SahanDissanayaka/Robot-Design-for-SLRC/Robo Arm/overall arm.SLDASM

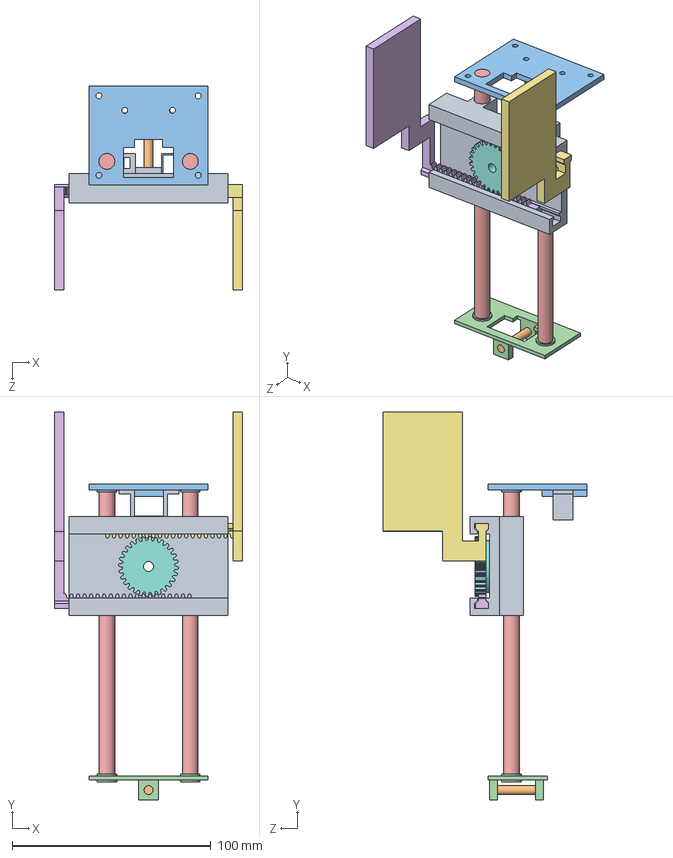
[picture p2: CAD file, 2024-04-25]
Robo Arm/overall arm.SLDASM
94.9 x 195.3 x 102.8 mm
base
Pinion Gear, Large Version
Pusher, 75mm Long left
Pusher, 75mm Long right
rod left x 2
upper base
lower base
pin upper
motor clip
