SahanDissanayaka/Robot-Design-for-SLRC/Robo Arm/Pusher, 75mm Long left.SLDPRT

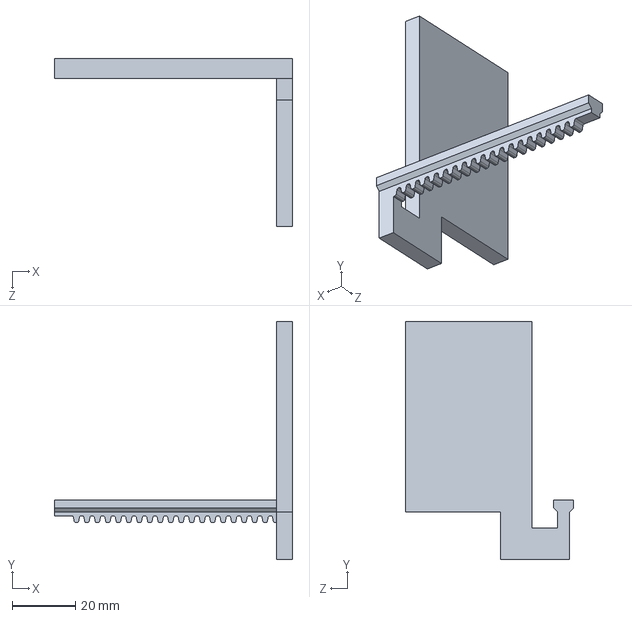
[picture p16: CAD file, 2024-04-25]
Robo Arm/Pusher, 75mm Long left.SLDPRT
75.0 x 75.0 x 53.1 mm
