SahanDissanayaka/Robot-Design-for-SLRC/SolidWorks/Enclosure/M3 Spacer MF 30mm.SLDPRT

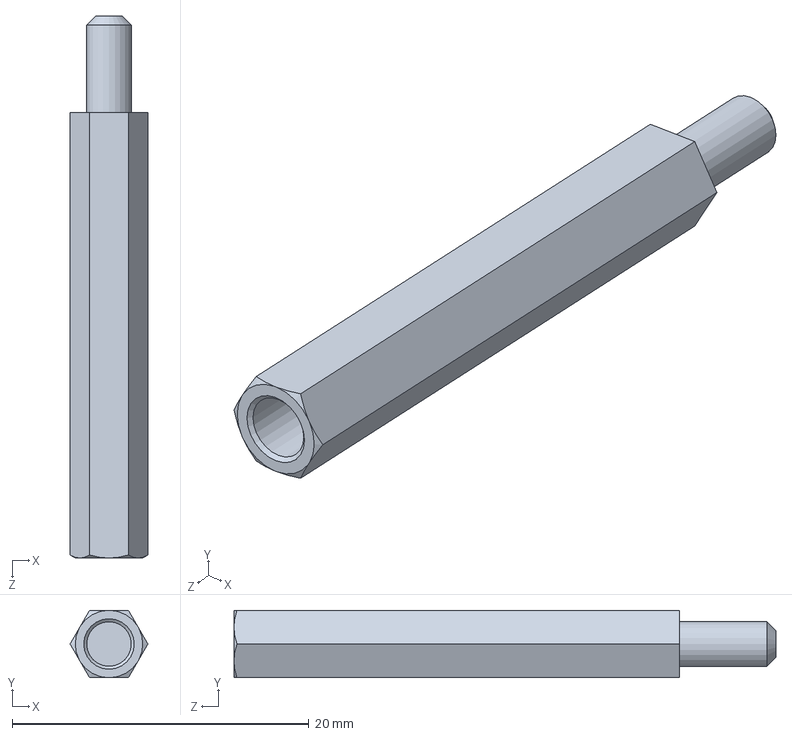
[picture p17: CAD file, 2024-04-28]
SolidWorks/Enclosure/M3 Spacer MF 30mm.SLDPRT
5.24 x 4.54 x 36.5 mm
