SahanDissanayaka/Robot-Design-for-SLRC/Robo Arm/motor clip.SLDPRT

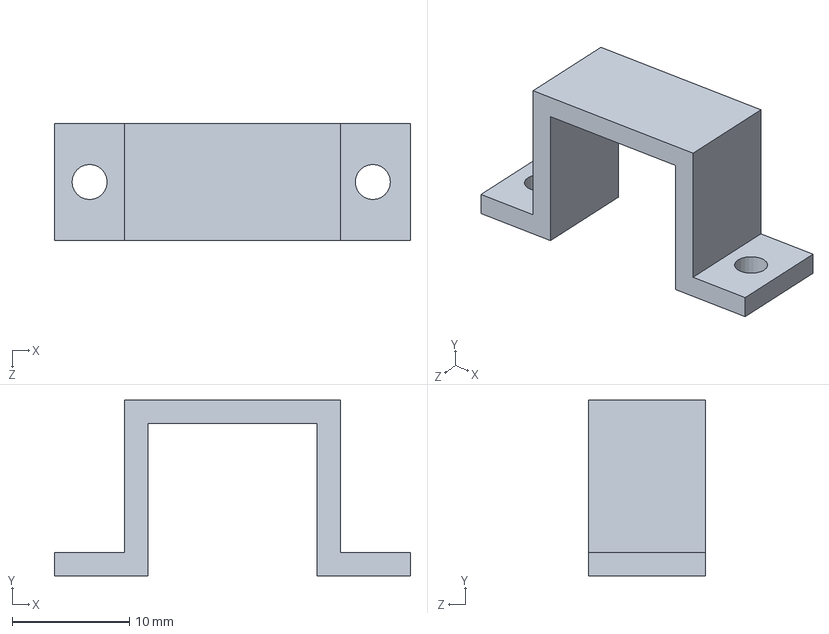
[picture p18: CAD file, 2024-04-25]
Robo Arm/motor clip.SLDPRT
30.4 x 15.0 x 10.0 mm
