SahanDissanayaka/Robot-Design-for-SLRC/SolidWorks/Enclosure/HCSR04 Ultrasonic Sensor.SLDPRT

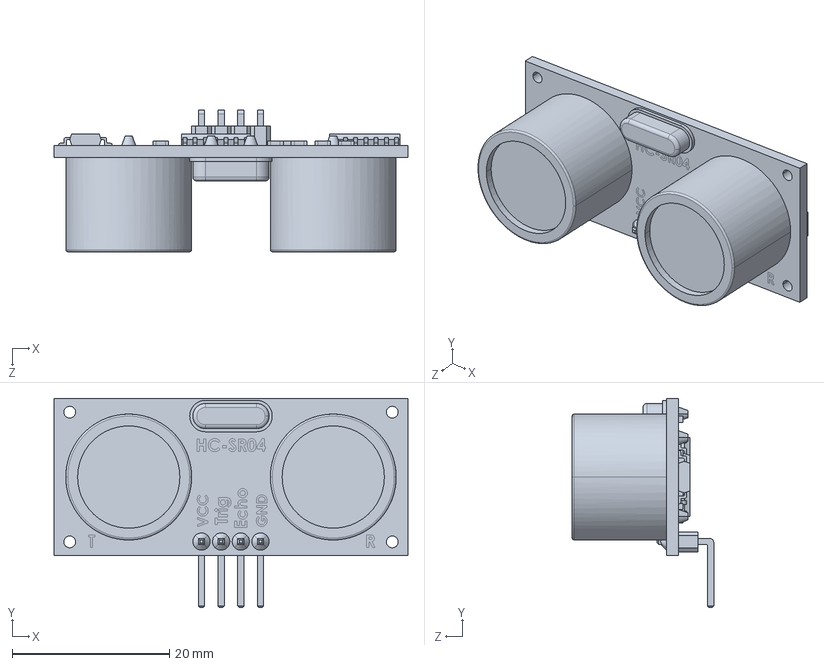
[picture p19: CAD file, 2024-04-28]
SolidWorks/Enclosure/HCSR04 Ultrasonic Sensor.SLDPRT
45.0 x 26.6 x 18.0 mm
