SahanDissanayaka/Robot-Design-for-SLRC/SolidWorks/Enclosure/IR holder.SLDPRT

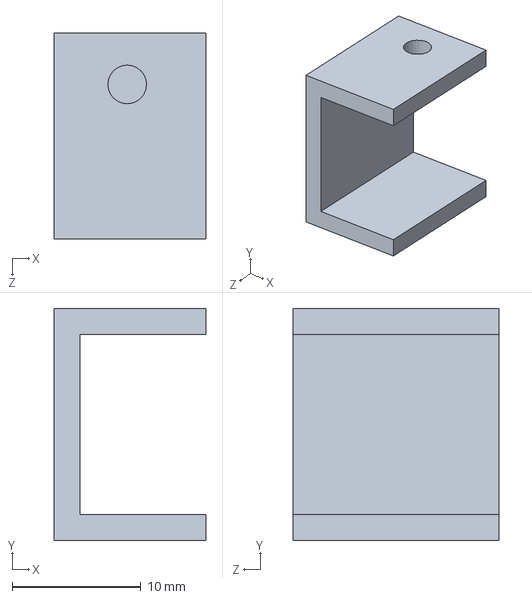
[picture p20: CAD file, 2024-04-28]
SolidWorks/Enclosure/IR holder.SLDPRT
11.8 x 18.0 x 16.0 mm
