SahanDissanayaka/Robot-Design-for-SLRC/Robo Arm/lower base.SLDPRT

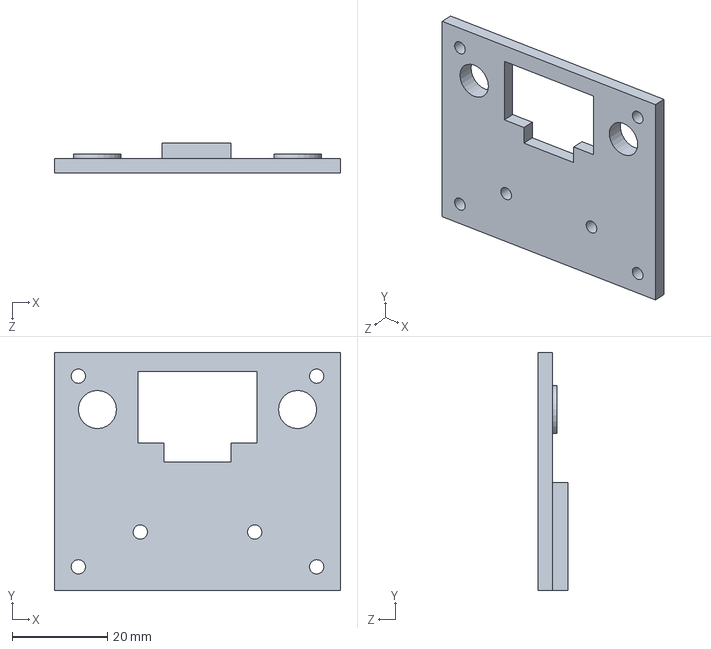
[picture p21: CAD file, 2024-04-25]
Robo Arm/lower base.SLDPRT
60.0 x 50.0 x 6.30 mm
