SahanDissanayaka/Robot-Design-for-SLRC/SolidWorks/Enclosure/ToF Holder.SLDPRT

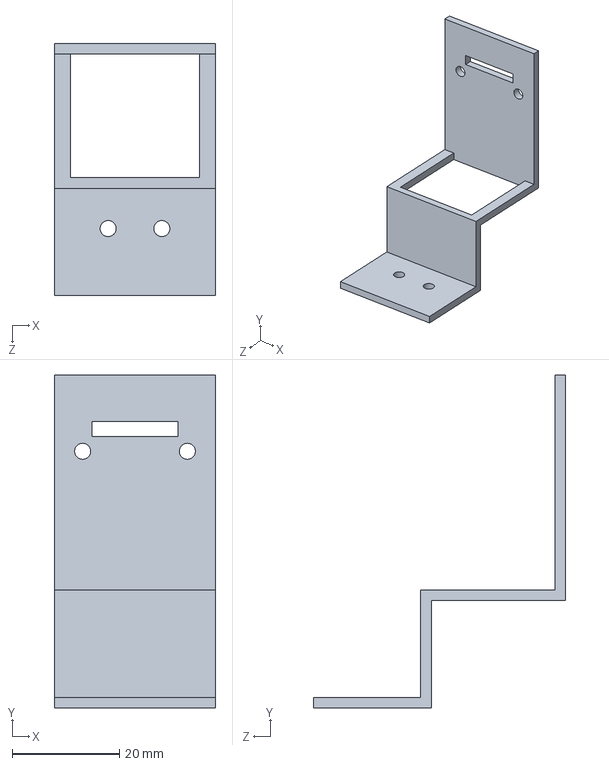
[picture p22: CAD file, 2024-04-28]
SolidWorks/Enclosure/ToF Holder.SLDPRT
30.0 x 62.0 x 47.0 mm
