SahanDissanayaka/Robot-Design-for-SLRC/Robo Arm/base.SLDPRT

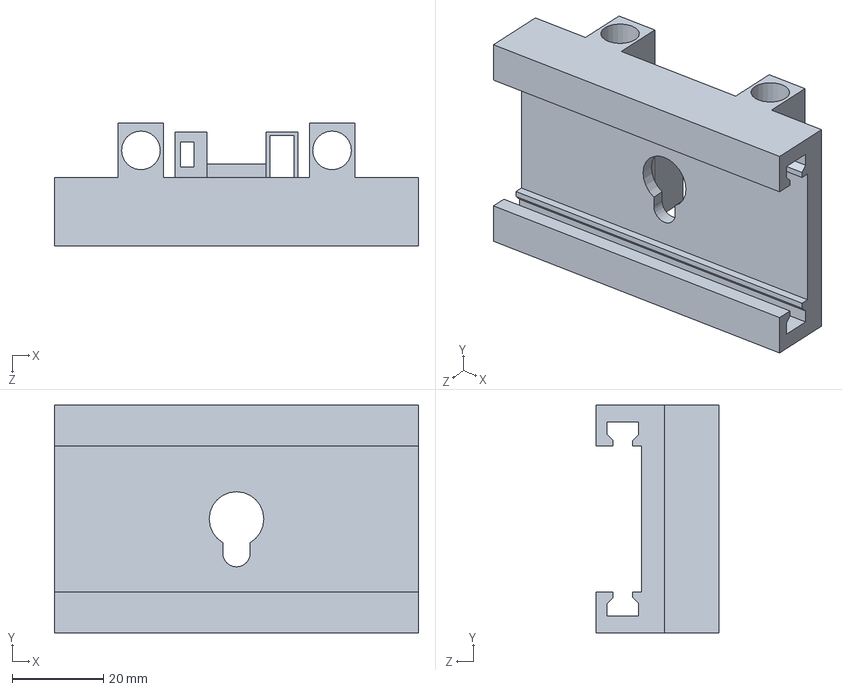
[picture p23: CAD file, 2024-04-25]
Robo Arm/base.SLDPRT
80.0 x 50.0 x 27.0 mm
