SahanDissanayaka/Robot-Design-for-SLRC/SolidWorks/Enclosure/Ultrasonic Holder.SLDPRT

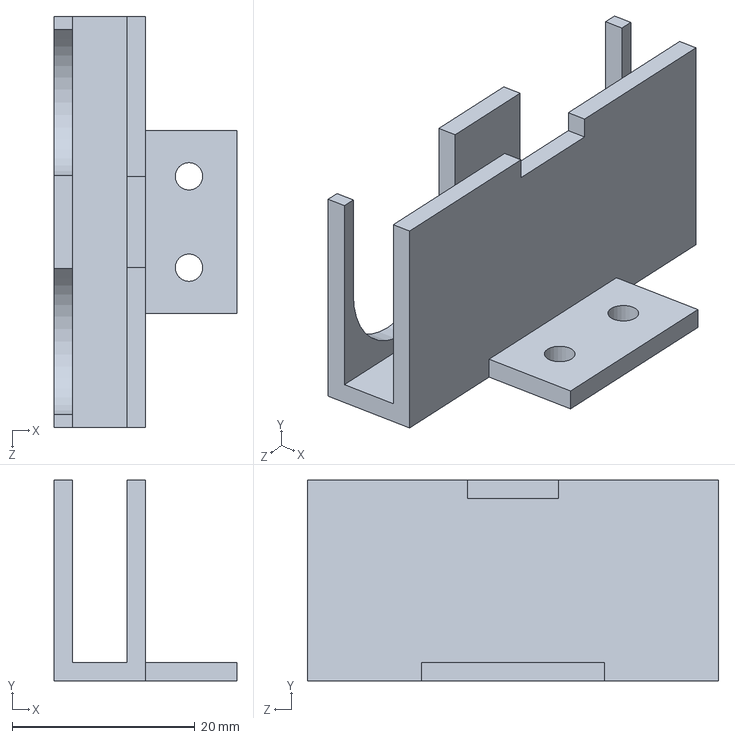
[picture p24: CAD file, 2024-04-28]
SolidWorks/Enclosure/Ultrasonic Holder.SLDPRT
20.0 x 22.0 x 45.0 mm
