SahanDissanayaka/Robot-Design-for-SLRC/Robo Arm/Pusher, 75mm Long right.SLDPRT

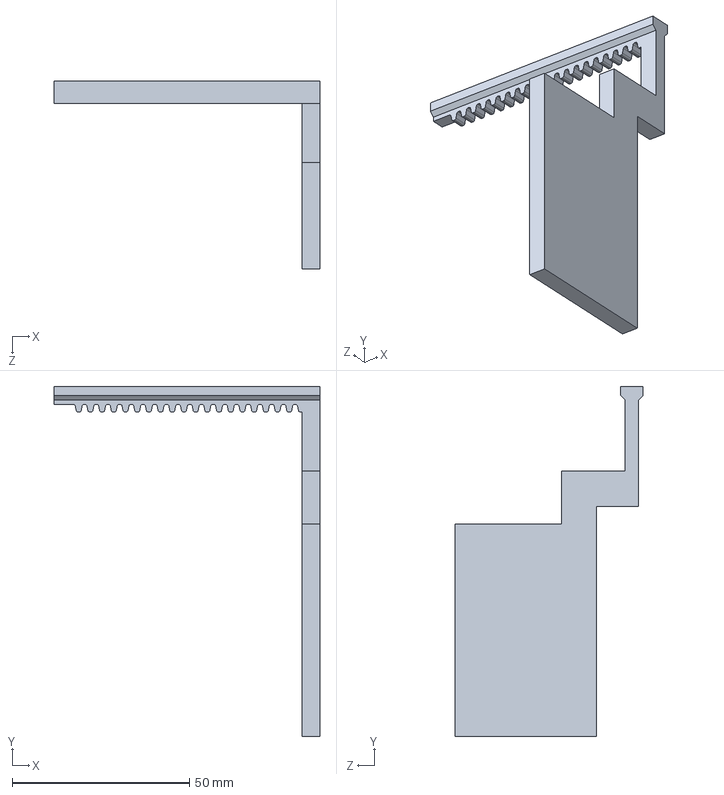
[picture p25: CAD file, 2024-04-25]
Robo Arm/Pusher, 75mm Long right.SLDPRT
75.0 x 98.8 x 53.1 mm
