SahanDissanayaka/Robot-Design-for-SLRC/SolidWorks/Enclosure/Top Part.SLDPRT

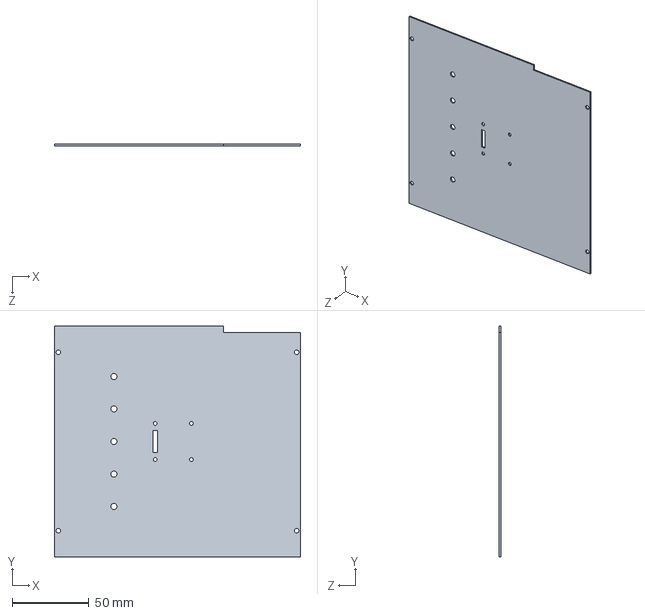
[picture p26: CAD file, 2024-04-28]
SolidWorks/Enclosure/Top Part.SLDPRT
160.0 x 150.0 x 1.00 mm
