SahanDissanayaka/Robot-Design-for-SLRC/Robo Arm/upper base.SLDPRT

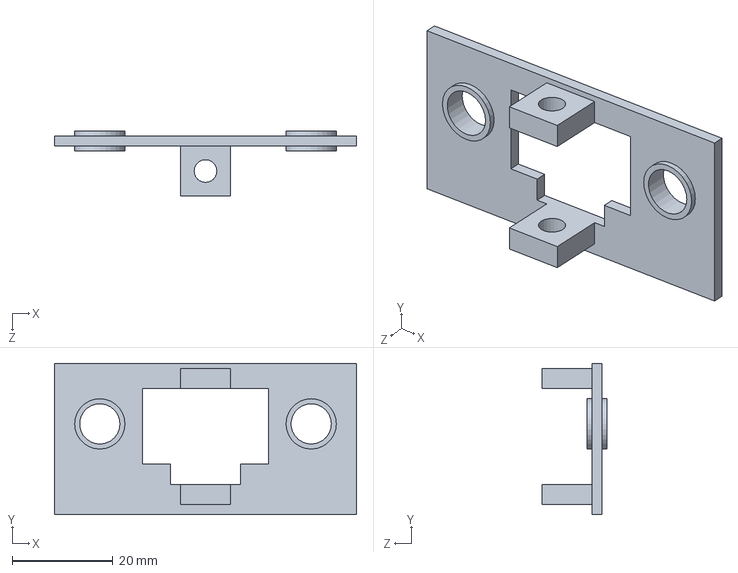
[picture p27: CAD file, 2024-04-25]
Robo Arm/upper base.SLDPRT
60.0 x 30.0 x 13.0 mm
