SahanDissanayaka/Robot-Design-for-SLRC/SolidWorks/Enclosure/TCS3200 color sensor.SLDPRT

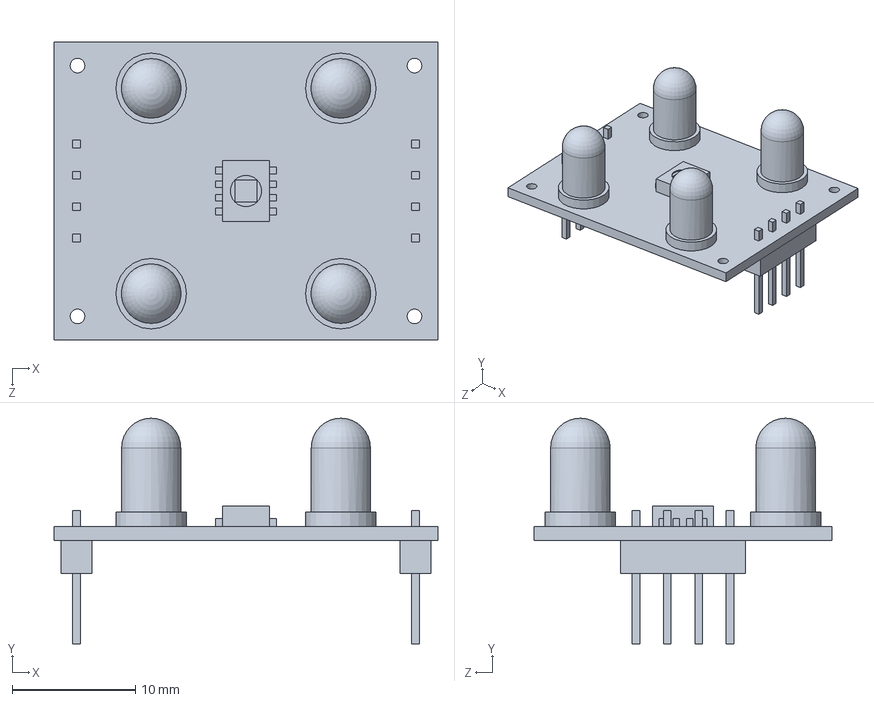
[picture p28: CAD file, 2024-04-28]
SolidWorks/Enclosure/TCS3200 color sensor.SLDPRT
31.1 x 18.3 x 24.1 mm
