SahanDissanayaka/Robot-Design-for-SLRC/SolidWorks/Enclosure/Chassis.SLDPRT

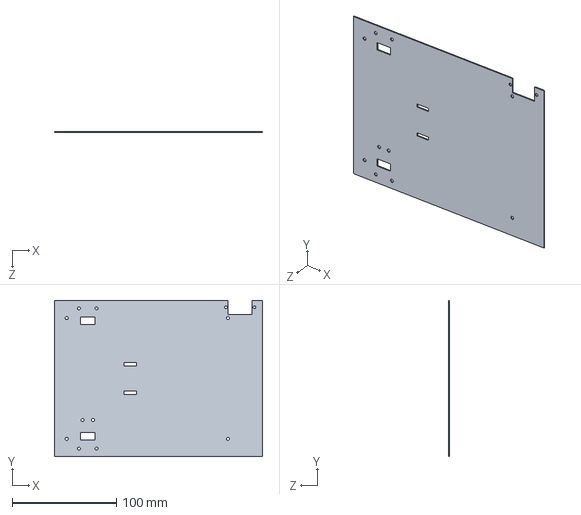
[picture p29: CAD file, 2024-04-28]
SolidWorks/Enclosure/Chassis.SLDPRT
200.0 x 150.0 x 1.00 mm
