SahanDissanayaka/Robot-Design-for-SLRC/SolidWorks/Enclosure/IR Array.SLDPRT

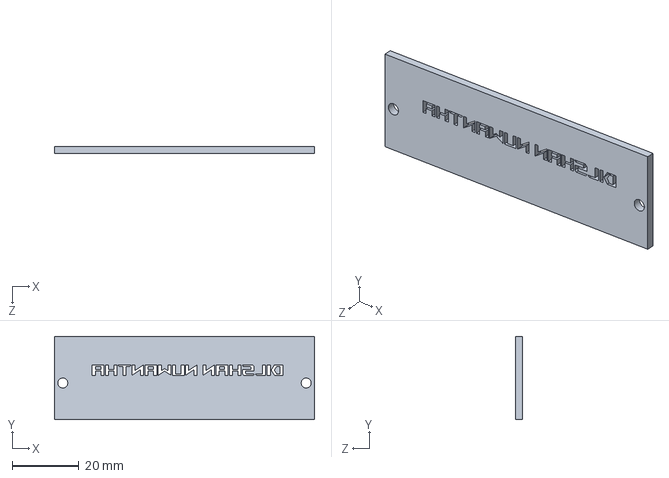
[picture p30: CAD file, 2024-04-28]
SolidWorks/Enclosure/IR Array.SLDPRT
78.0 x 25.0 x 2.00 mm
